JordanAceto/stereo_whooshy_sound/hardware/jack_panel/docs/2D/individual_layers/stereo_whooshy_sound_jack_panel-Edge_Cuts.pdf

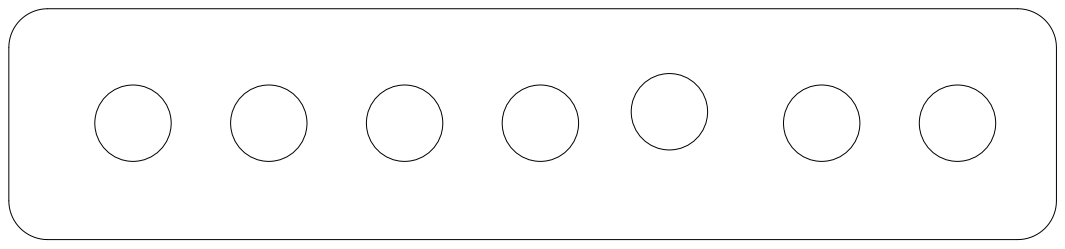
[picture p33: page 1]
