JordanAceto/stereo_whooshy_sound/hardware/jack_panel/docs/2D/individual_layers/stereo_whooshy_sound_jack_panel-F_Cu.pdf

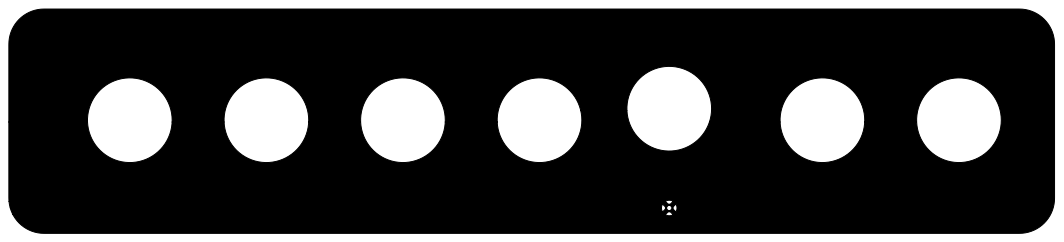
[picture p34: page 1]
