JordanAceto/stereo_whooshy_sound/hardware/jack_panel/docs/2D/individual_layers/stereo_whooshy_sound_jack_panel-F_Fab.pdf

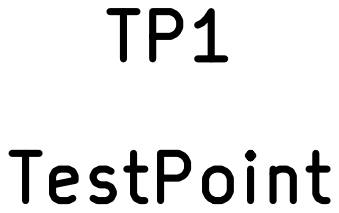
[picture p35: page 1]
