JordanAceto/stereo_whooshy_sound/hardware/front_panel/docs/2D/individual_layers/stereo_whooshy_sound_front_panel-B_Cu.pdf

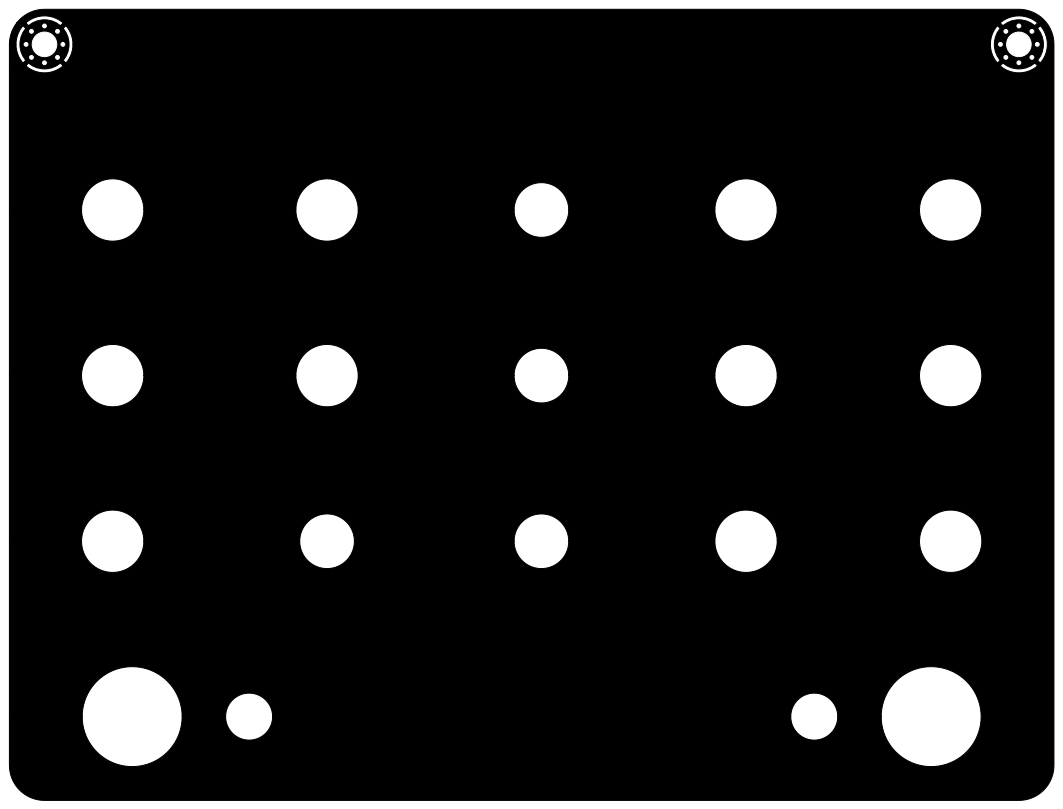
[picture p37: page 1]
