JordanAceto/stereo_whooshy_sound/hardware/front_panel/docs/2D/individual_layers/stereo_whooshy_sound_front_panel-Edge_Cuts.pdf

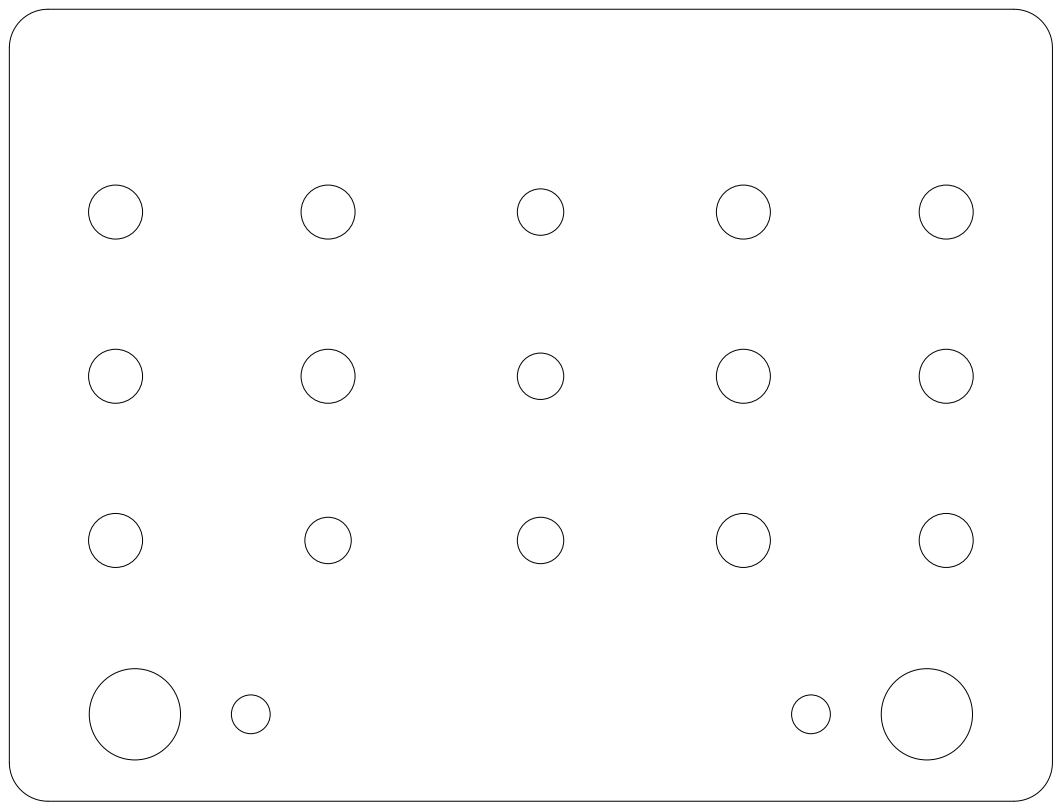
[picture p38: page 1]
