JordanAceto/stereo_whooshy_sound/hardware/front_panel/docs/2D/individual_layers/stereo_whooshy_sound_front_panel-F_Silkscreen.pdf

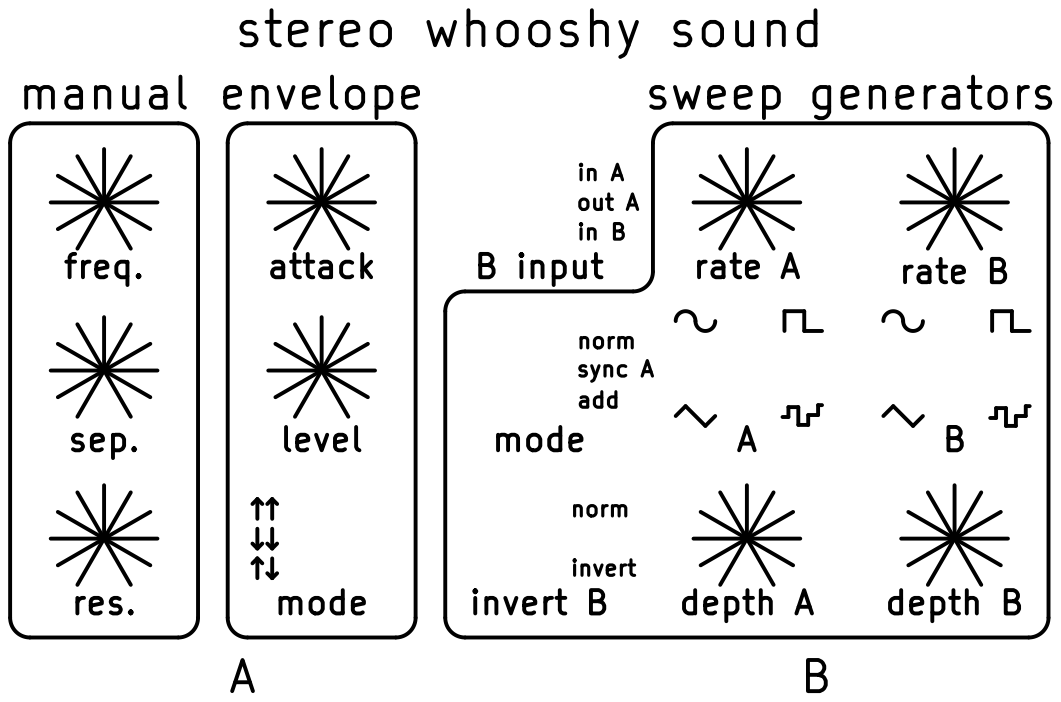
[picture p39: page 1]
